JRNitre/JoystickFreeJoy/img/img_04.jpg

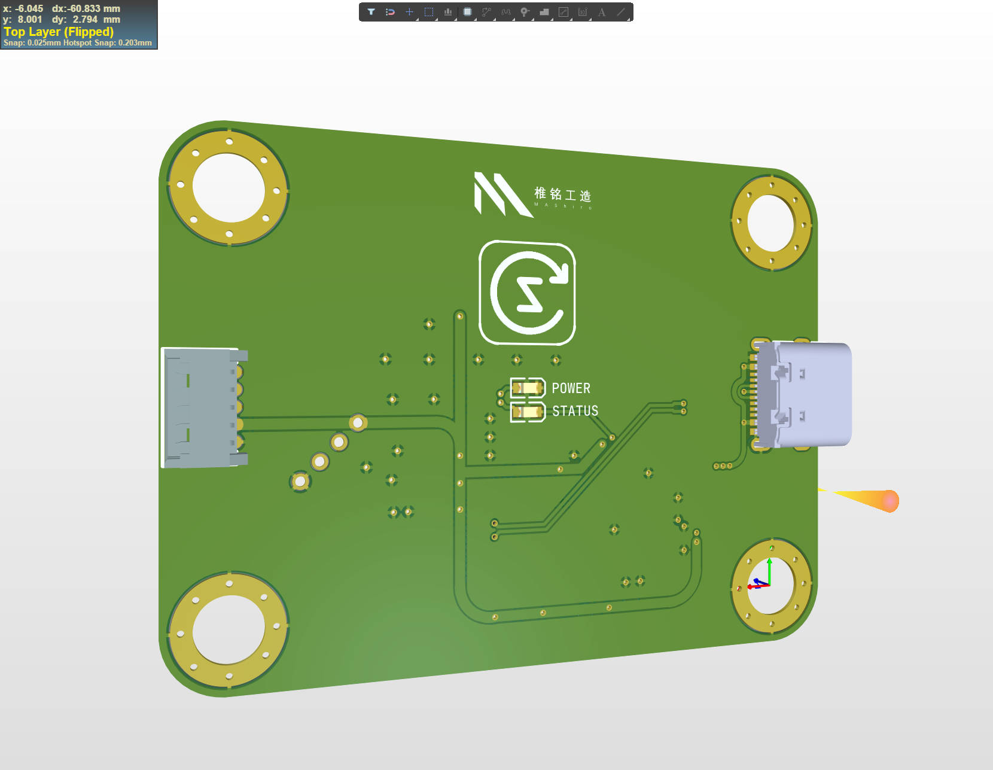
img/img_04.jpg
