JRNitre/JoystickFreeJoy/model/FDM 打印优化/solidworks2022_sldprt/joystick_base_回中组件_V1.0.SLDPRT

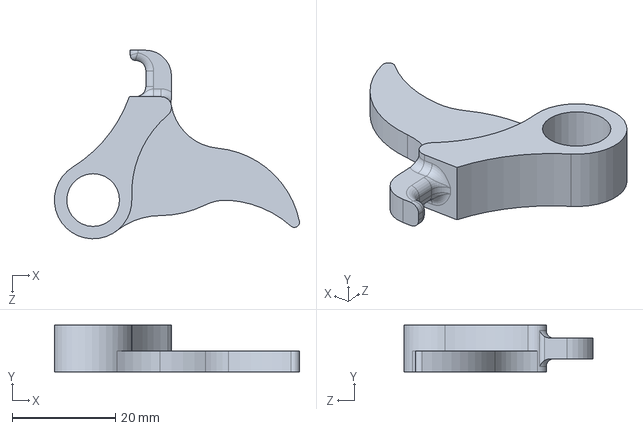
[picture p15: CAD file, 2025-05-08]
model/FDM 打印优化/solidworks2022_sldprt/joystick_base_回中组件_V1.0.SLDPRT
47.4 x 9.00 x 36.5 mm
