JRNitre/JoystickFreeJoy/model/stand/joystick_base_stl/joystick_base_顶板_V1.0.STL

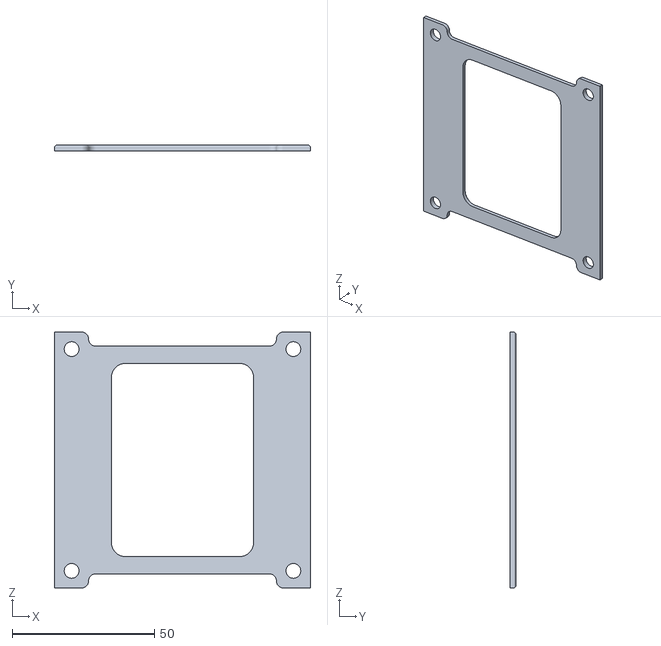
[picture p16: CAD file, 2025-10-08]
model/stand/joystick_base_stl/joystick_base_顶板_V1.0.STL
90.0 x 2.00 x 90.0
