JRNitre/JoystickFreeJoy/model/FDM 打印优化/solidworks2022_sldprt/joystick_base_摇杆座_V1.0.SLDPRT

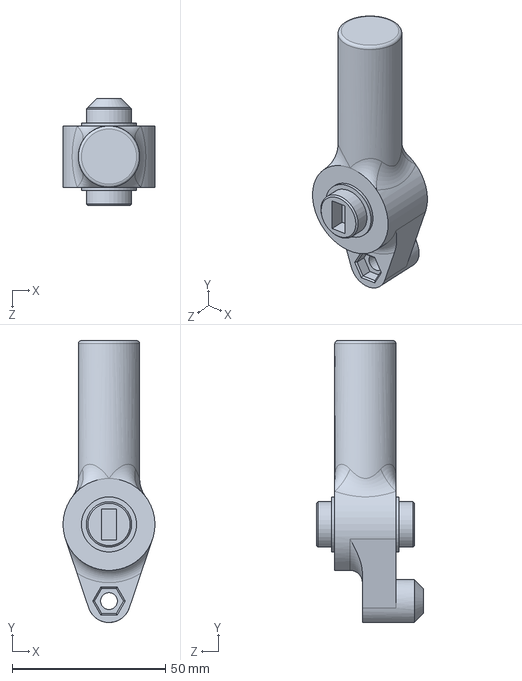
[picture p17: CAD file, 2025-05-08]
model/FDM 打印优化/solidworks2022_sldprt/joystick_base_摇杆座_V1.0.SLDPRT
30.0 x 92.0 x 35.0 mm
