JRNitre/JoystickFreeJoy/model/FDM 打印优化/solidworks2022_sldprt/joystick_base_Y-钳位固定件B_V1.0.SLDPRT

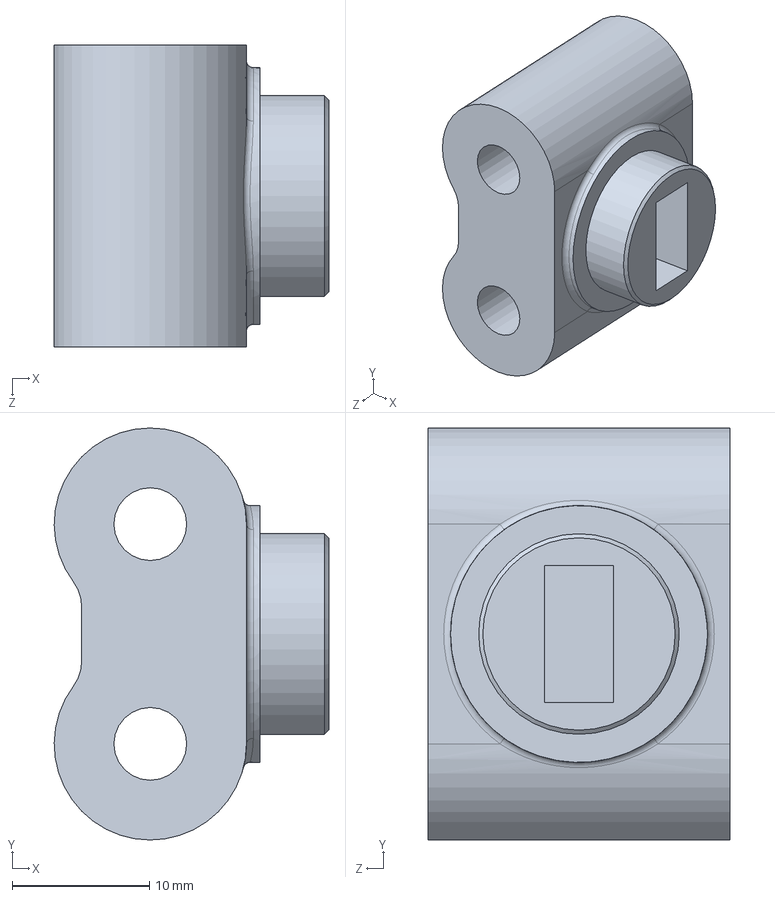
[picture p18: CAD file, 2025-05-08]
model/FDM 打印优化/solidworks2022_sldprt/joystick_base_Y-钳位固定件B_V1.0.SLDPRT
20.0 x 30.0 x 22.0 mm
