JRNitre/JoystickFreeJoy/model/stand/solidworks2022_sldprt/joystick_base_Y-钳位固定件B_V1.0.SLDPRT

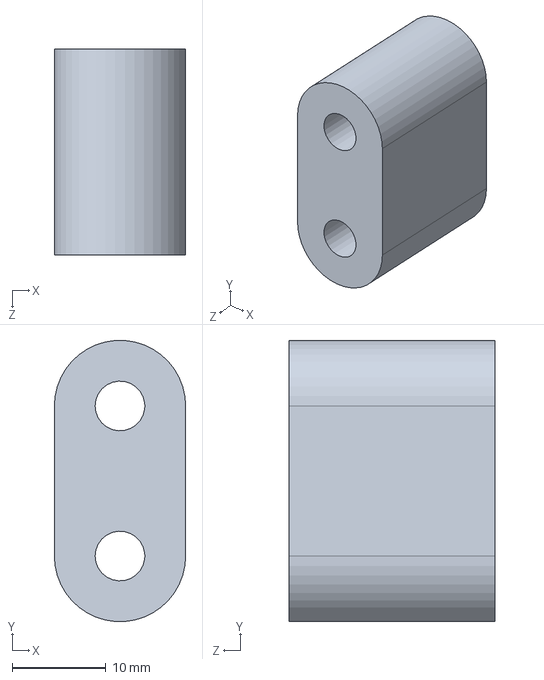
[picture p19: CAD file, 2025-05-08]
model/stand/solidworks2022_sldprt/joystick_base_Y-钳位固定件B_V1.0.SLDPRT
14.0 x 30.0 x 22.0 mm
